drChungus/VCSequentialSwitch/Photoshooting/homebckgnd.jpg

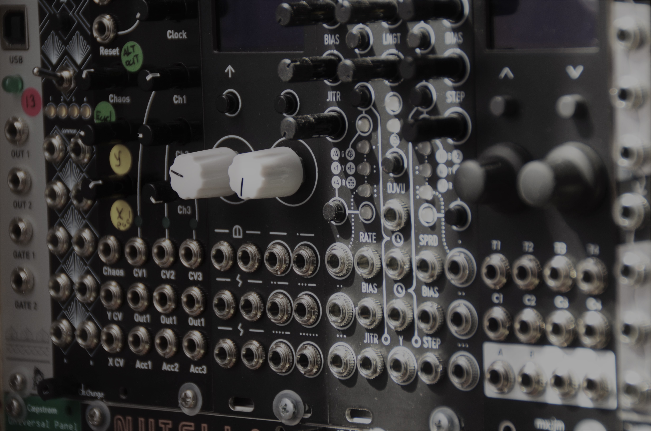
Photoshooting/homebckgnd.jpg
