drChungus/VCSequentialSwitch/resources/IMG_20210507_070857.jpg

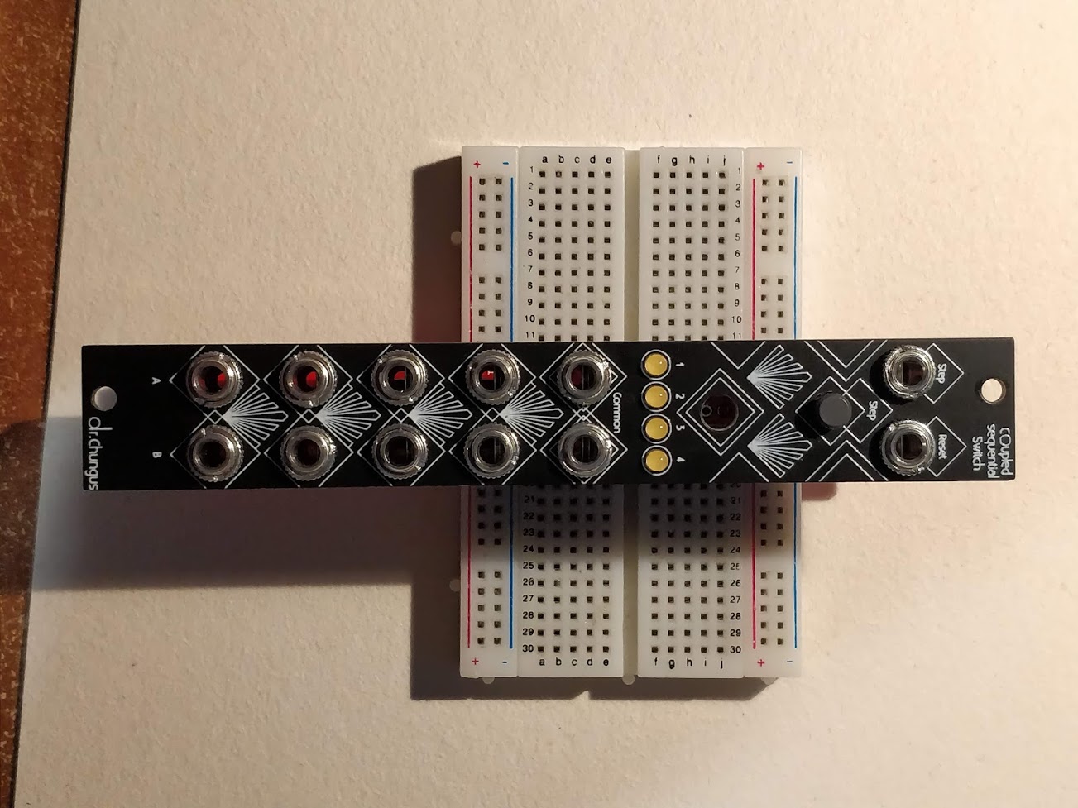
resources/IMG_20210507_070857.jpg
