drChungus/VCSequentialSwitch/resources/IMG_20210507_070857crop.jpg

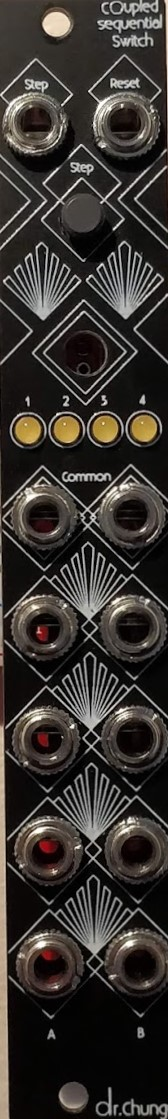
resources/IMG_20210507_070857crop.jpg
