drChungus/VCSequentialSwitch/resources/seqswitch_545.gif

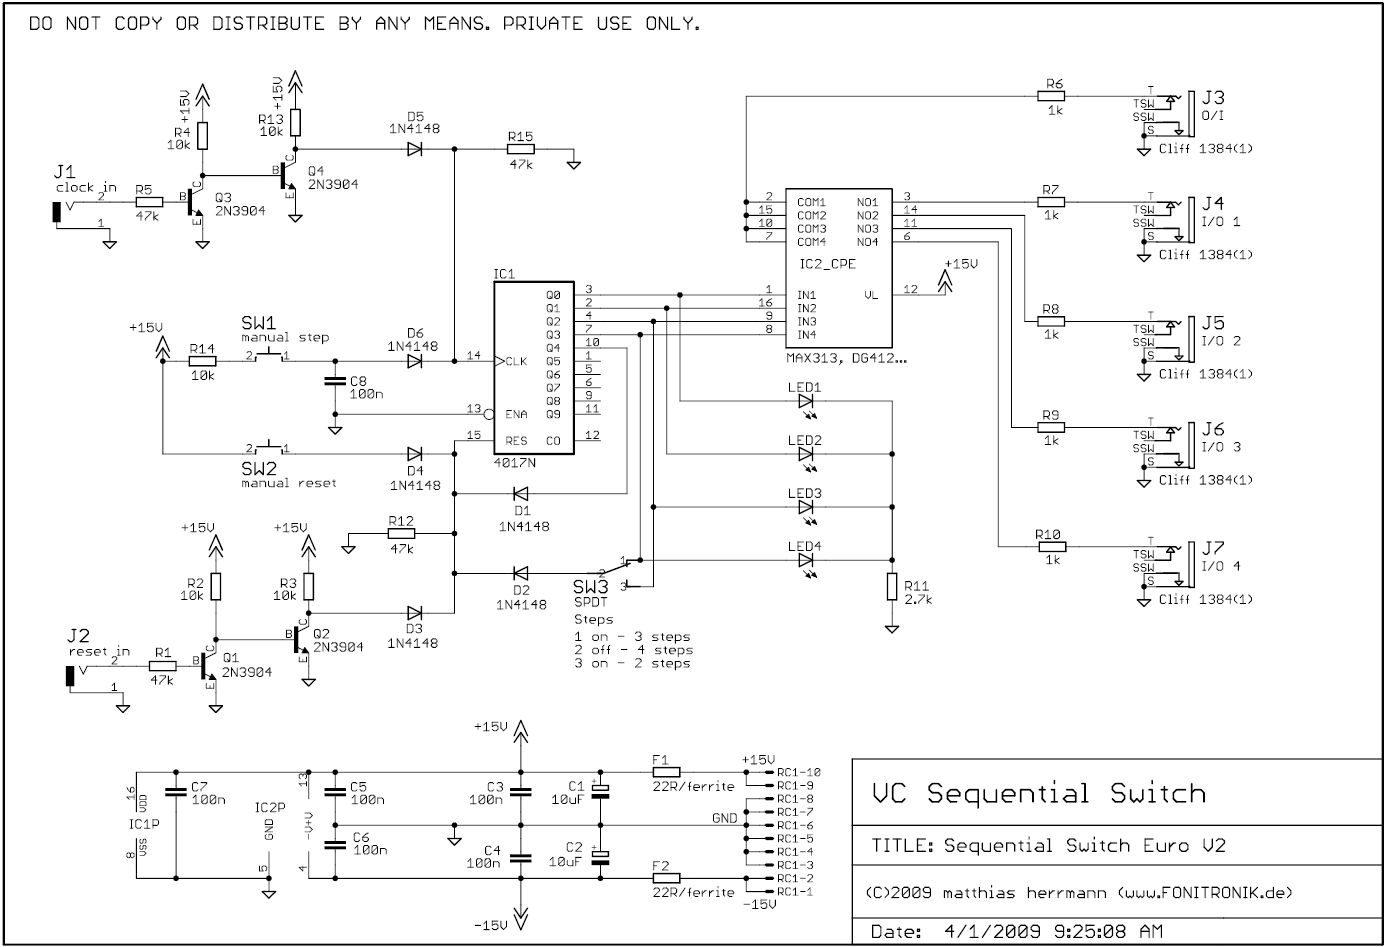
resources/seqswitch_545.gif
