drChungus/VCSequentialSwitch/resources/tinrsTools/QuickRender/BoardPlateAfterDrills.png

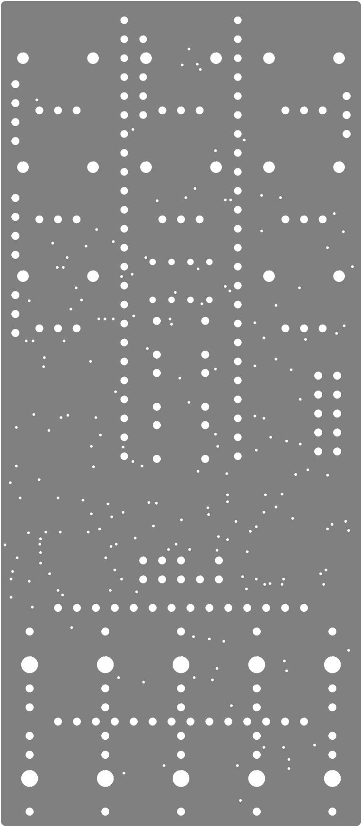
resources/tinrsTools/QuickRender/BoardPlateAfterDrills.png
