drChungus/VCSequentialSwitch/resources/tinrsTools/QuickRender/Bottom_copper.png

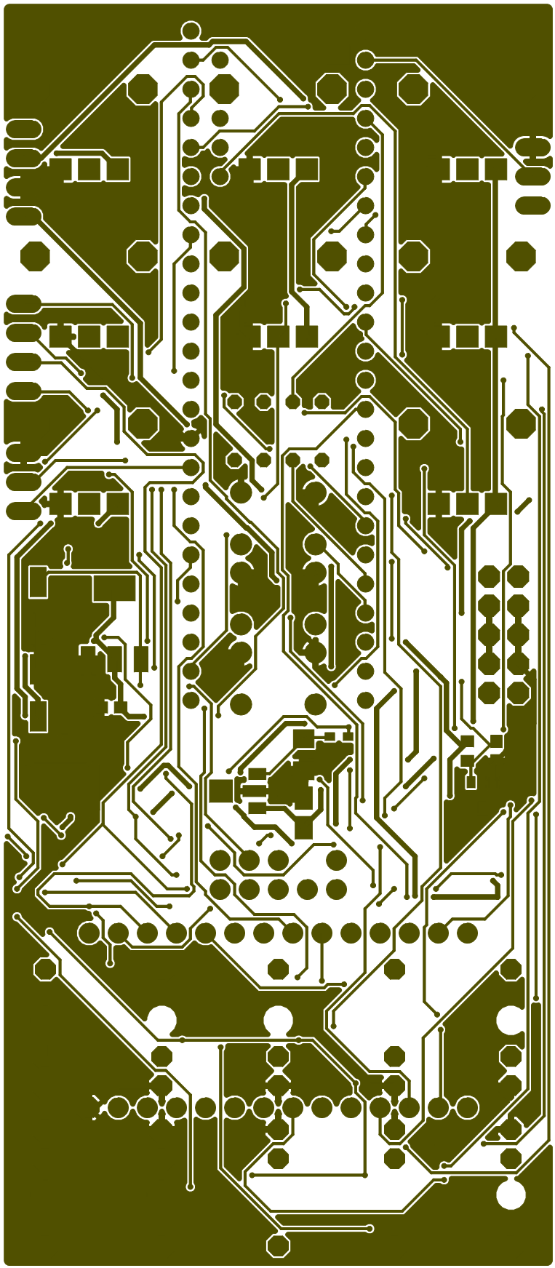
resources/tinrsTools/QuickRender/Bottom_copper.png
