drChungus/VCSequentialSwitch/resources/tinrsTools/QuickRender/Bottom_drill.png

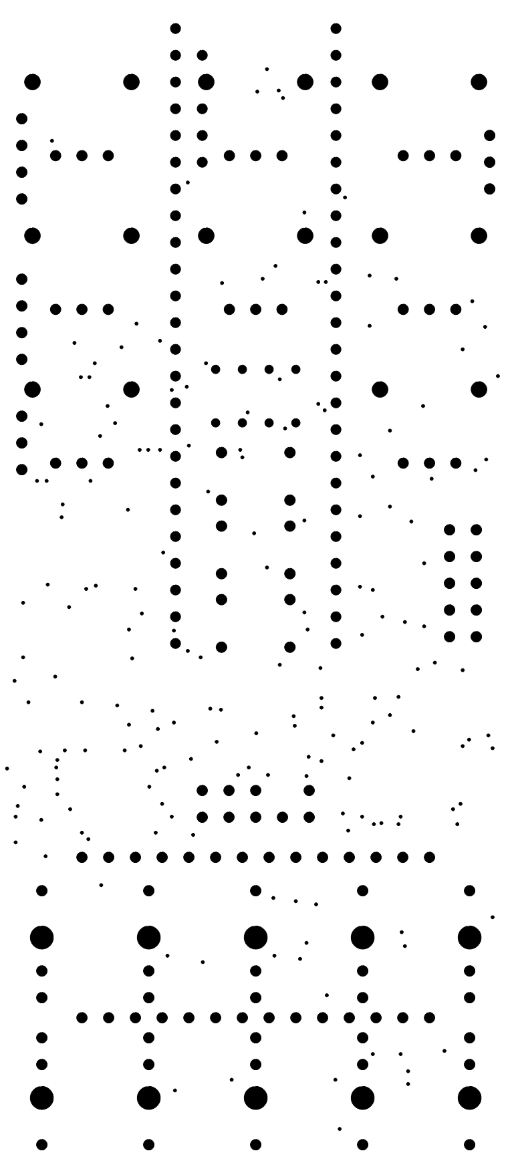
resources/tinrsTools/QuickRender/Bottom_drill.png
