drChungus/VCSequentialSwitch/resources/tinrsTools/QuickRender/FinalAfterCopper.png

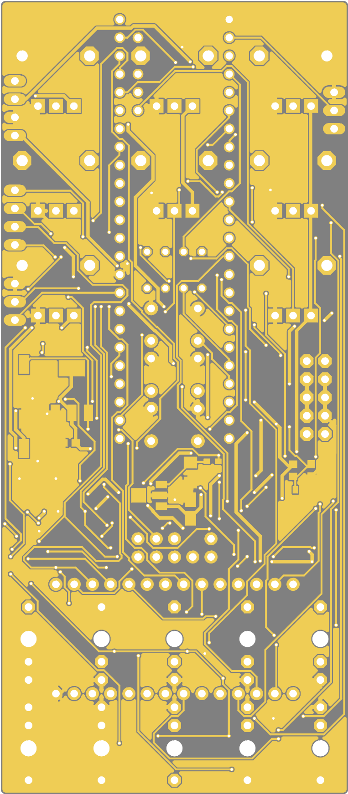
resources/tinrsTools/QuickRender/FinalAfterCopper.png
