drChungus/VCSequentialSwitch/resources/tinrsTools/QuickRender/Top_base.png

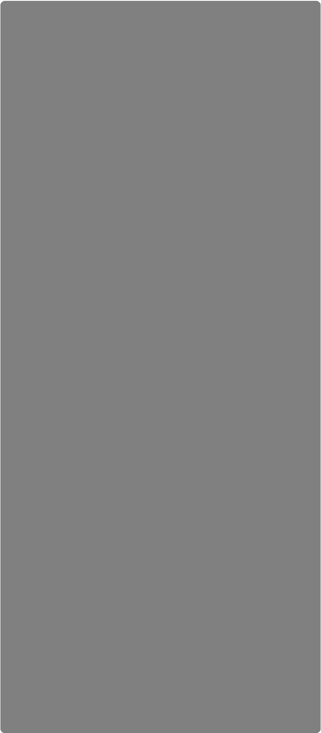
resources/tinrsTools/QuickRender/Top_base.png
