drChungus/VCSequentialSwitch/resources/tinrsTools/QuickRender/Top_copper.png

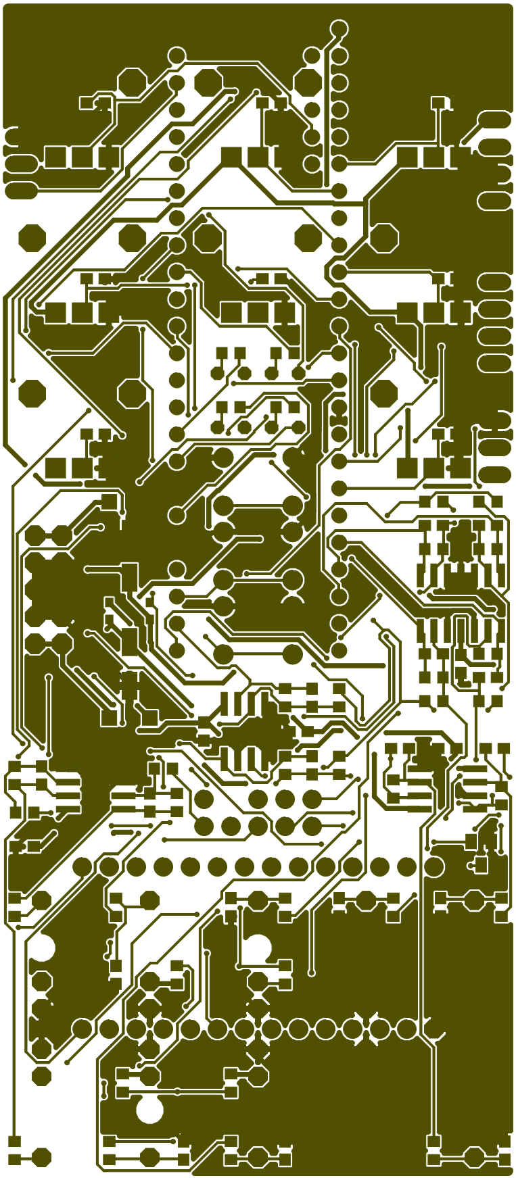
resources/tinrsTools/QuickRender/Top_copper.png
