drChungus/VCSequentialSwitch/resources/tinrsTools/QuickRender/Top_drill.png

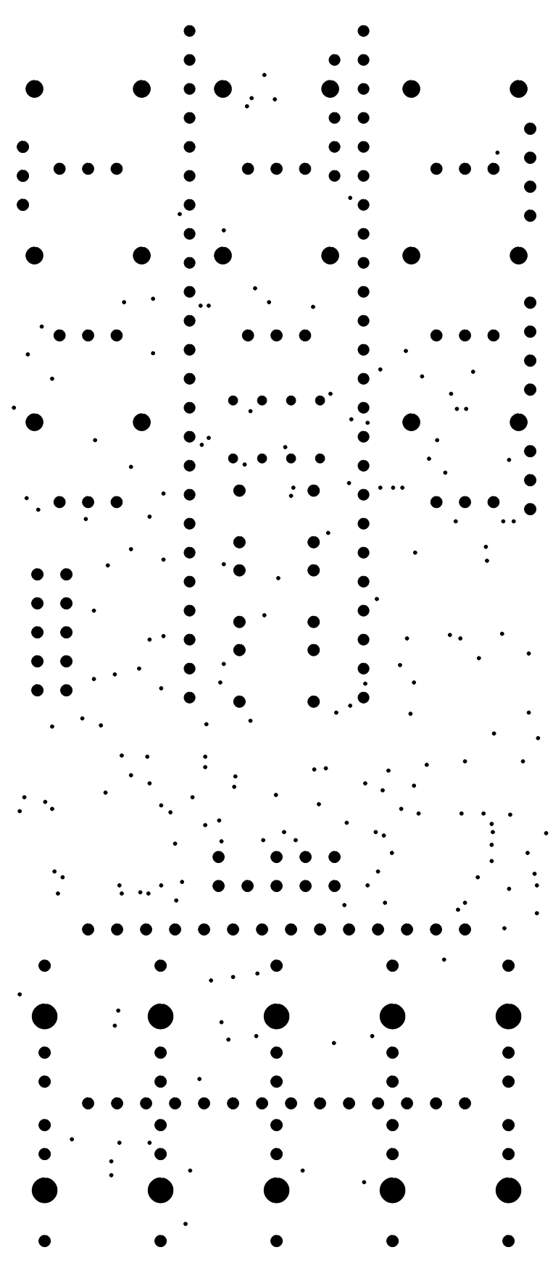
resources/tinrsTools/QuickRender/Top_drill.png
