drChungus/VCSequentialSwitch/resources/tinrsTools/QuickRender/Bottom_soldermaskholes.png

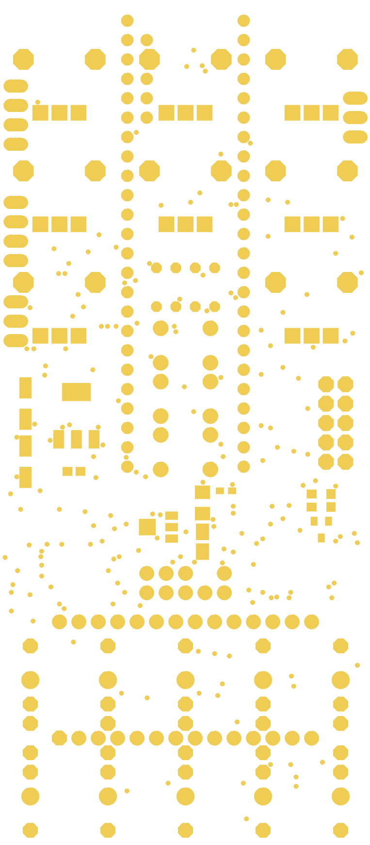
resources/tinrsTools/QuickRender/Bottom_soldermaskholes.png
