drChungus/VCSequentialSwitch/resources/tinrsTools/QuickRender/FinalAfterSoldermask.png

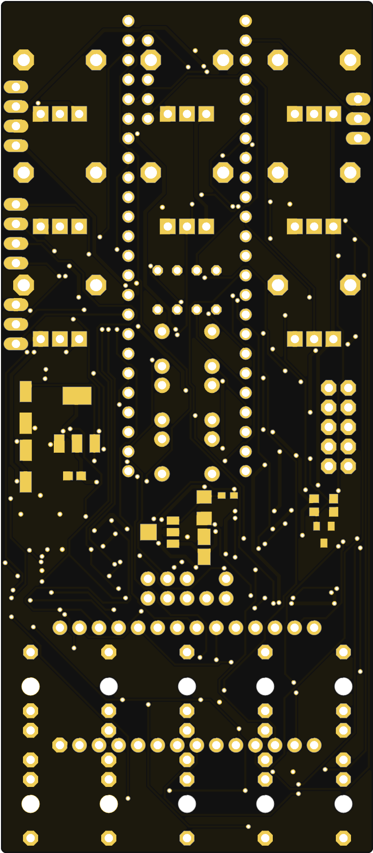
resources/tinrsTools/QuickRender/FinalAfterSoldermask.png
