drChungus/VCSequentialSwitch/resources/tinrsTools/QuickRender/Top_soldermaskholes.png

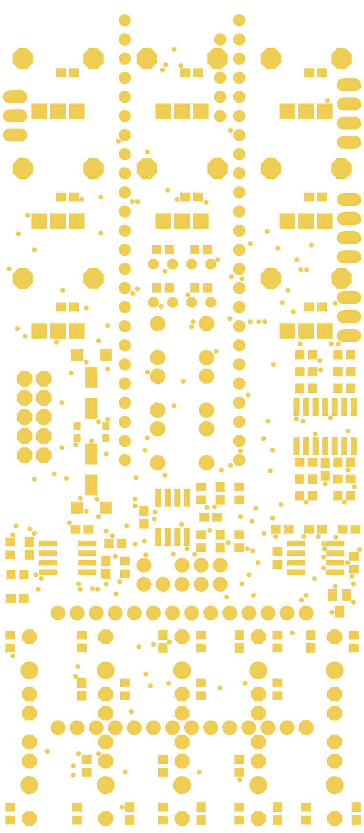
resources/tinrsTools/QuickRender/Top_soldermaskholes.png
